ThorstenBr/AppleIII_diskII/ebay/AppleIII_scp_change_drives.jpg

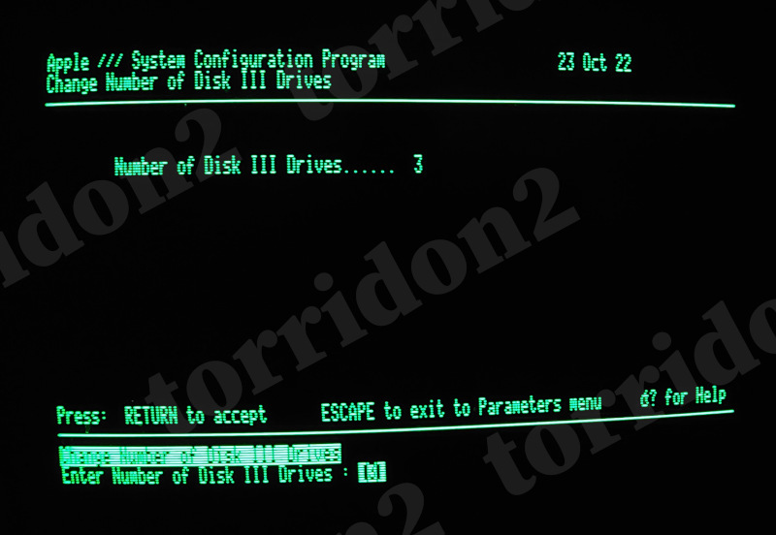
ebay/AppleIII_scp_change_drives.jpg
